DaComputerNerd717/DVC-Sensor/videoserver.py

#!/usr/bin/python3

# Mostly copied from https://picamera.readthedocs.io/en/release-1.13/recipes2.html
# Run this script, then point a web browser at http:<this-ip-address>:8000
# Note: needs simplejpeg to be installed (pip3 install simplejpeg).

import io
import logging
import socketserver
from http import server
from threading import Condition
from picamera2 import Picamera2
from picamera2.encoders import JpegEncoder
from picamera2.outputs import FileOutput
import argparse
import cv2
import numpy as np
import tflite_runtime.interpreter as tflite
from picamera2 import MappedArray, Picamera2, Preview

PAGE = """\
<html>
<head>
<title>picamera2 MJPEG streaming demo</title>
</head>
<body>
<h1>Picamera2 MJPEG Streaming Demo</h1>
<img src="stream.mjpg" width="640" height="480" />
</body>
</html>
"""

normalSize = (640, 480)
lowresSize = (320, 240)

rectangles = []


def ReadLabelFile(file_path):
    with open(file_path, 'r') as f:
        lines = f.readlines()
    ret = {}
    for line in lines:
        pair = line.strip().split(maxsplit=1)
        ret[int(pair[0])] = pair[1].strip()
    return ret


def DrawRectangles(request):
    with MappedArray(request, "main") as m:
        for rect in rectangles:
            rect_start = (int(rect[0] * 2) - 5, int(rect[1] * 2) - 5)
            rect_end = (int(rect[2] * 2) + 5, int(rect[3] * 2) + 5)
            cv2.rectangle(m.array, rect_start, rect_end, (0, 255, 0, 0))


def InferenceTensorFlow(image, model, output, label=None):
    global rectangles

    if label:
        labels = ReadLabelFile(label)
    else:
        labels = None

    interpreter = tflite.Interpreter(model_path=model, num_threads=4)
    interpreter.allocate_tensors()

    input_details = interpreter.get_input_details()
    output_details = interpreter.get_output_details()
    height = input_details[0]['shape'][1]
    width = input_details[0]['shape'][2]
    floating_model = False
    if input_details[0]['dtype'] == np.float32:
        floating_model = True

    rgb = cv2.cvtColor(image, cv2.COLOR_GRAY2RGB)
    initial_h, initial_w, channels = rgb.shape

    picture = cv2.resize(rgb, (width, height))

    input_data = np.expand_dims(picture, axis=0)
    if floating_model:
        input_data = (np.float32(input_data) - 127.5) / 127.5

    interpreter.set_tensor(input_details[0]['index'], input_data)

    interpreter.invoke()
    #print(output_details)
    detected_boxes = interpreter.get_tensor(output_details[0]['index'])
    detected_classes = interpreter.get_tensor(output_details[1]['index'])
    detected_scores = interpreter.get_tensor(output_details[2]['index'])
    num_boxes = interpreter.get_tensor(output_details[3]['index'])

    rectangles = []
    for i in range(int(num_boxes)):
        top, left, bottom, right = detected_boxes[0][i]
        classId = int(detected_classes[0][i])
        score = detected_scores[0][i]
        if score > 0.5:
            xmin = left * initial_w
            ymin = bottom * initial_h
            xmax = right * initial_w
            ymax = top * initial_h
            if labels:
                print(labels[classId], 'score = ', score)
            else:
                print('score = ', score)
            box = [xmin, ymin, xmax, ymax]
            rectangles.append(box)

class StreamingOutput(io.BufferedIOBase):
    def __init__(self):
        self.frame = None
        self.condition = Condition()

    def write(self, buf):
        with self.condition:
            self.frame = buf
            self.condition.notify_all()


class StreamingHandler(server.BaseHTTPRequestHandler):
    def do_GET(self):
        output_file = 'out.jpg'
        label_file = "coco_labels.txt"
        if self.path == '/':
            self.send_response(301)
            self.send_header('Location', '/index.html')
            self.end_headers()
        elif self.path == '/index.html':
            content = PAGE.encode('utf-8')
            self.send_response(200)
            self.send_header('Content-Type', 'text/html')
            self.send_header('Content-Length', len(content))
            self.end_headers()
            self.wfile.write(content)
        elif self.path == '/stream.mjpg':
            self.send_response(200)
            self.send_header('Age', 0)
            self.send_header('Cache-Control', 'no-cache, private')
            self.send_header('Pragma', 'no-cache')
            self.send_header('Content-Type', 'multipart/x-mixed-replace; boundary=FRAME')
            self.end_headers()
            try:
                while True:
                    buffer = picam2.capture_buffer("lores")
                    grey = buffer[:stride * lowresSize[1]].reshape((lowresSize[1], stride))
                    _ = InferenceTensorFlow(grey, "mobilenet_v2.tflite", output_file, label_file)

                    with output.condition:
                        output.condition.wait()
                        frame = output.frame
                    self.wfile.write(b'--FRAME\r\n')
                    self.send_header('Content-Type', 'image/jpeg')
                    self.send_header('Content-Length', len(frame))
                    self.end_headers()
                    self.wfile.write(frame)
                    self.wfile.write(b'\r\n')
            except Exception as e:
                logging.warning('Removed streaming client %s: %s',self.client_address, str(e))
                pass
        else:
            self.send_error(404)
            self.end_headers()


class StreamingServer(socketserver.ThreadingMixIn, server.HTTPServer):
    allow_reuse_address = True
    daemon_threads = True


picam2 = Picamera2()
picam2.configure(picam2.create_video_configuration(main={"size": (640, 480)},lores={"size": lowresSize, "format": "YUV420"}))
stride = picam2.stream_configuration("lores")["stride"]
picam2.post_callback = DrawRectangles
output = StreamingOutput()
picam2.start_recording(JpegEncoder(), FileOutput(output))

try:
    address = ('', 8000)
    server = StreamingServer(address, StreamingHandler)
    server.serve_forever()
finally:
    picam2.stop_recording()
